bitelxux/chimenea-2000/data/chimenea.png

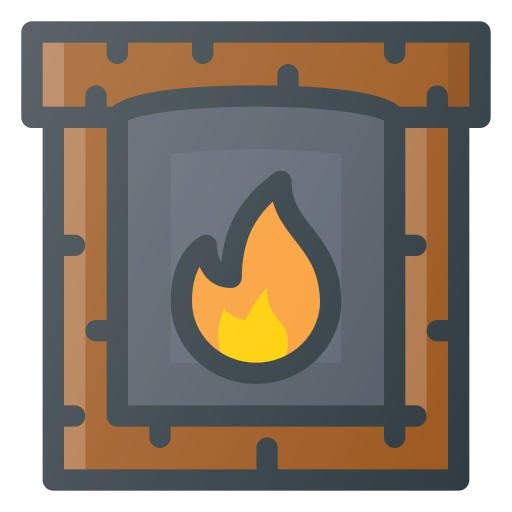
data/chimenea.png
